edgex004/KeyV2/src/key_profiles.scad

// key profile definitions

// unlike the other files with their own dedicated folders, this one doesn't
// need a selector. I wrote one anyways for customizer support though
include <key_profiles/dcs.scad>
include <key_profiles/oem.scad>
include <key_profiles/dsa.scad>
include <key_profiles/sa.scad>
include <key_profiles/g20.scad>
include <key_profiles/loprolilly.scad>
include <key_profiles/hipro.scad>
include <key_profiles/grid.scad>

// man, wouldn't it be so cool if functions were first order
module key_profile(key_profile_type, row, column=0) {
  if (key_profile_type == "dcs") {
    dcs_row(row, column) children();
  } else if (key_profile_type == "oem") {
    oem_row(row, column) children();
  } else if (key_profile_type == "dsa") {
    dsa_row(row, column) children();
  } else if (key_profile_type == "sa") {
    sa_row(row, column) children();
  } else if (key_profile_type == "g20") {
    g20_row(row, column) children();
  } else if (key_profile_type == "loprolilly") {
    loprolilly_row(row, column) children();
  } else if (key_profile_type == "hipro") {
    hipro_row(row, column) children();
  } else if (key_profile_type == "grid") {
    grid_row(row, column) children();
  } else if (key_profile_type == "disable") {
    children();
  } else {
    echo("Warning: unsupported key_profile_type");
  }
}
